rprakitpong/Beefy-Cabbage-punches-the-Queen/step4 - 3DP final files/standPanel-1.stl

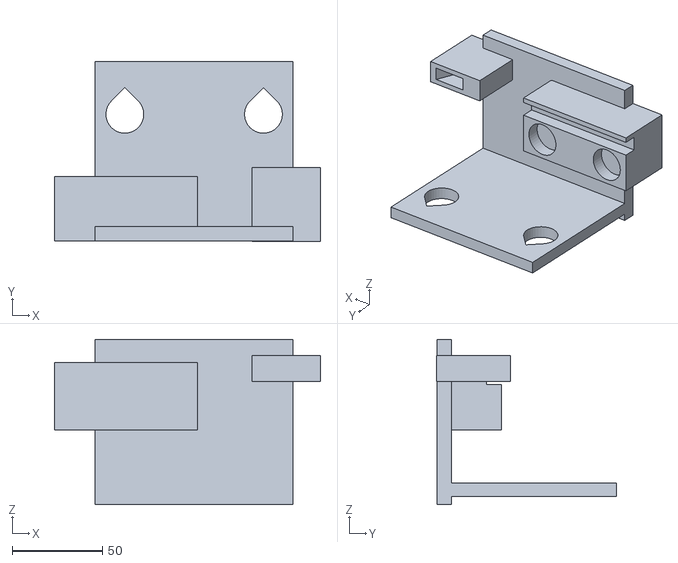
[picture p17: CAD file, 2019-01-07]
step4 - 3DP final files/standPanel-1.stl
147.7 x 99.7 x 91.9
