rprakitpong/Beefy-Cabbage-punches-the-Queen/step3 - blender/FilesFromSldr - panelStand-1.STL

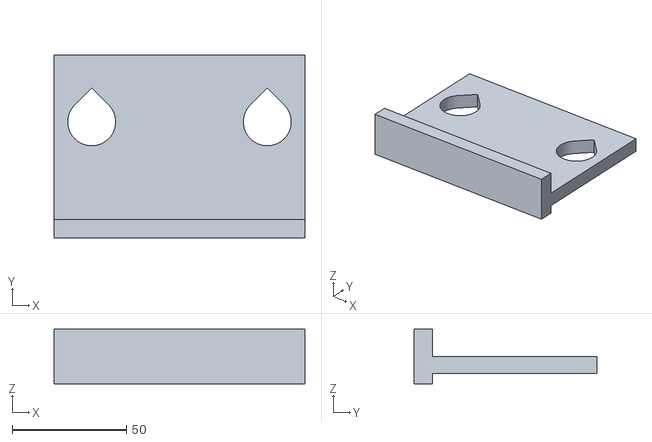
[picture p18: CAD file, 2019-01-07]
step3 - blender/FilesFromSldr - panelStand-1.STL
110.0 x 80.0 x 24.0
