rprakitpong/Beefy-Cabbage-punches-the-Queen/step4 - 3DP final files/muscularArmShaft.stl

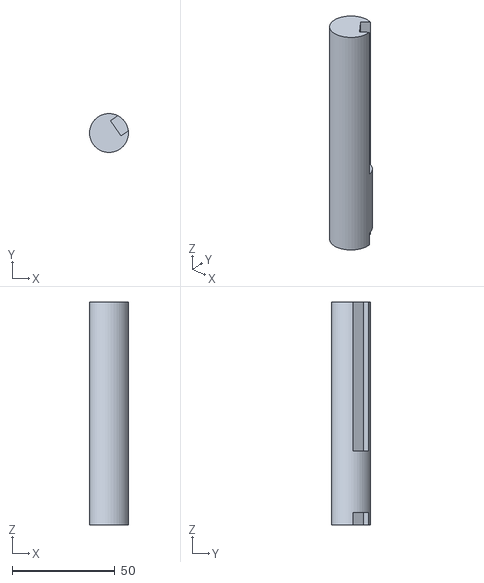
[picture p19: CAD file, 2019-01-07]
step4 - 3DP final files/muscularArmShaft.stl
19.0 x 19.0 x 108.8
