rprakitpong/Beefy-Cabbage-punches-the-Queen/step3 - blender/FilesFromSldr - Gear System-1 Gear Design Tutorial-1.STL

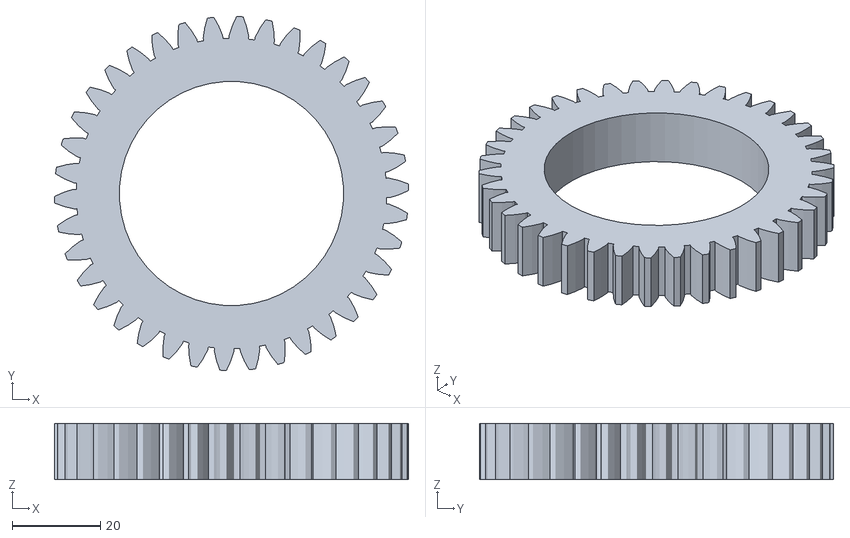
[picture p20: CAD file, 2019-01-06]
step3 - blender/FilesFromSldr - Gear System-1 Gear Design Tutorial-1.STL
80.2 x 80.2 x 12.7
