rprakitpong/Beefy-Cabbage-punches-the-Queen/step4 - 3DP final files/queenHeadWithCamAligner-1.stl

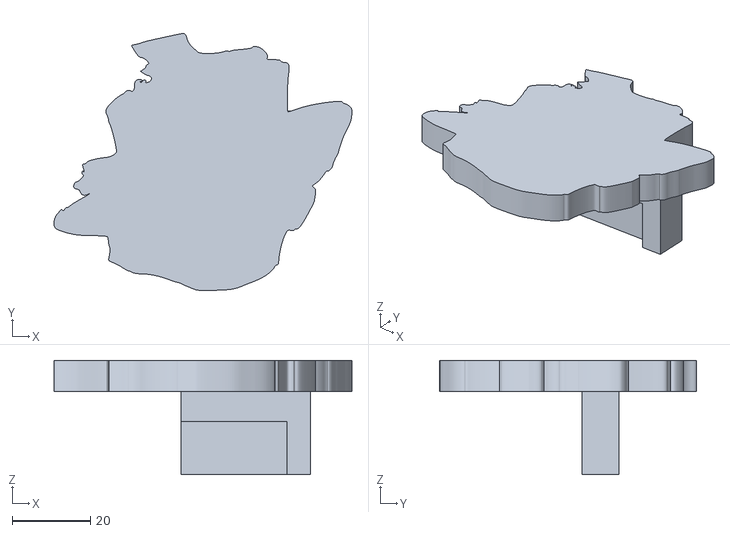
[picture p21: CAD file, 2019-01-06]
step4 - 3DP final files/queenHeadWithCamAligner-1.stl
76.2 x 65.7 x 29.2
