rprakitpong/Beefy-Cabbage-punches-the-Queen/step4 - 3DP final files/cabbageWithStand-1.stl

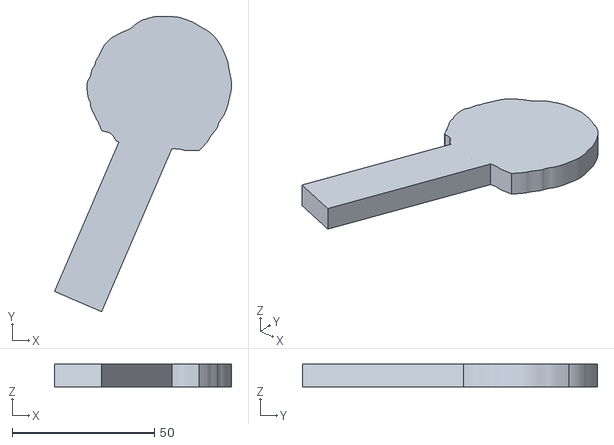
[picture p22: CAD file, 2019-01-06]
step4 - 3DP final files/cabbageWithStand-1.stl
62.2 x 103.9 x 8.01
