rprakitpong/Beefy-Cabbage-punches-the-Queen/step4 - 3DP final files/queenBody-1.stl

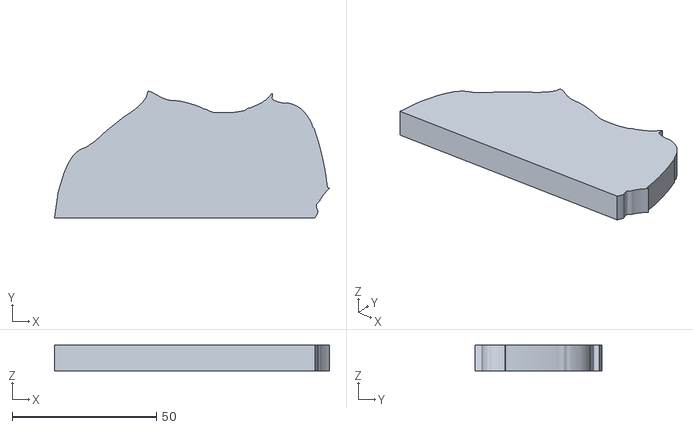
[picture p23: CAD file, 2019-01-06]
step4 - 3DP final files/queenBody-1.stl
95.4 x 43.9 x 9.00
