rprakitpong/Beefy-Cabbage-punches-the-Queen/step2 - paint.net/cabbage-nobackground-black-2by2in.png

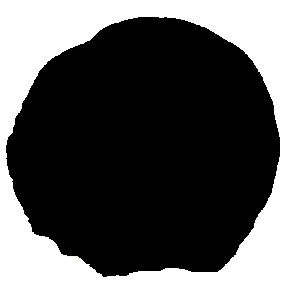
step2 - paint.net/cabbage-nobackground-black-2by2in.png
