rprakitpong/Beefy-Cabbage-punches-the-Queen/step2 - paint.net/muscular arm-reference.jpg

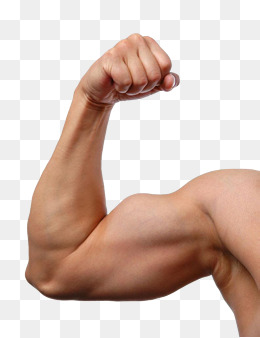
step2 - paint.net/muscular arm-reference.jpg
