rprakitpong/Beefy-Cabbage-punches-the-Queen/step2 - paint.net/muscular-arm-nobackgournd-3by2in.png

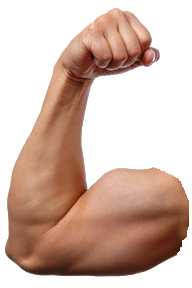
step2 - paint.net/muscular-arm-nobackgournd-3by2in.png
