rprakitpong/Beefy-Cabbage-punches-the-Queen/step2 - paint.net/queen-headonly-nobackgournd-3by3in.png

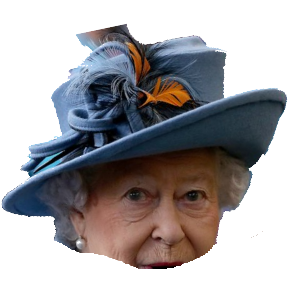
step2 - paint.net/queen-headonly-nobackgournd-3by3in.png
