rprakitpong/Beefy-Cabbage-punches-the-Queen/step2 - paint.net/queen-nohead-nobackground-5by4in.png

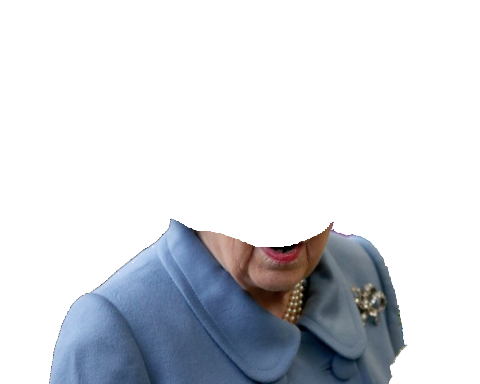
step2 - paint.net/queen-nohead-nobackground-5by4in.png
