rprakitpong/Beefy-Cabbage-punches-the-Queen/step2 - paint.net/queen-nohead-nobackground-black-5by4in.png

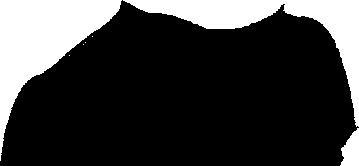
step2 - paint.net/queen-nohead-nobackground-black-5by4in.png
